qbancoffee/coco_motherboards/26-313xB/3d_models/channel_switch.stp

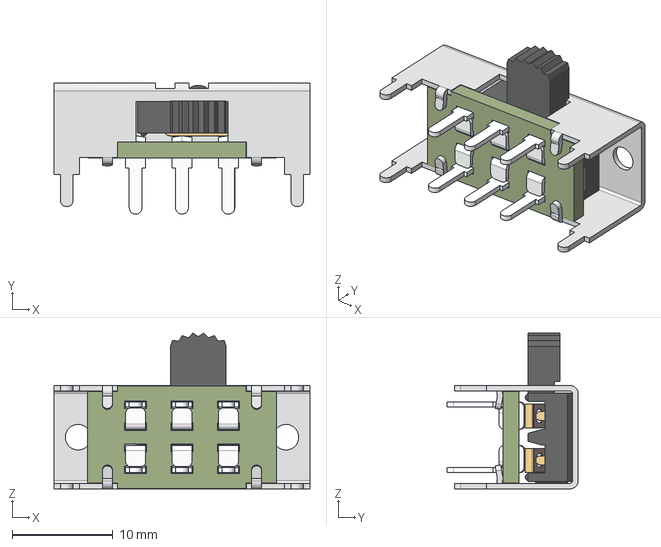
[picture p18: CAD file, 2022-07-08]
26-313xB/3d_models/channel_switch.stp
25.4 x 13.0 x 15.5 mm
