qbancoffee/coco_motherboards/26-313xB/3d_models/keyboard_connector.stp

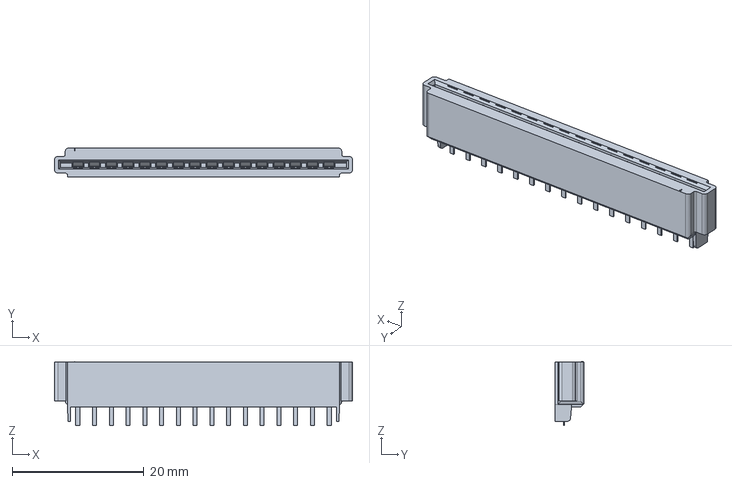
[picture p19: CAD file, 2022-07-08]
26-313xB/3d_models/keyboard_connector.stp
45.2 x 4.39 x 9.73 mm
