qbancoffee/coco_motherboards/26-313xB/3d_models/power_post.STEP

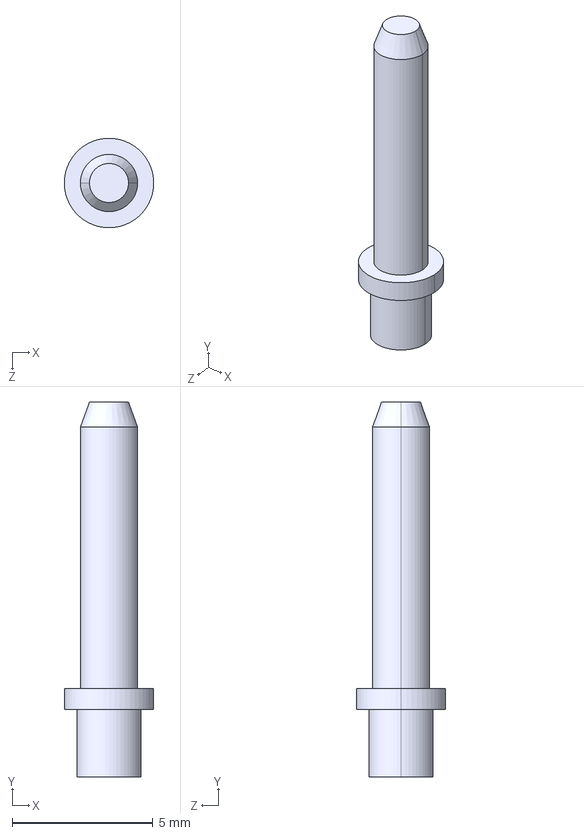
[picture p20: CAD file, 2022-07-08]
26-313xB/3d_models/power_post.STEP
3.18 x 13.3 x 3.18 mm
