qbancoffee/coco_motherboards/26-313xA/coco2/coco2.sch

## KiCad design 26-313xA/coco2/coco2.sch (2022-08-04)

Schematic: coco2.sch

Parts:
C1: .1uF; C_Disc_D4.7mm_W2.5mm_P5.00mm; Manufacturer part# RDER71H104K0K1H03B
CN1: Conn_02x20_Odd_Even; EBC20DRAS; Manufacturer part# EBC20DRAS
H999002, H999003: MountingHole; MountingHole_4mm
LOGO1: coco2_3134x_layout; coco2_3134A_layout
LOGO2: coco2_3134x_layout_top; coco2_3134A_layout_top
LOGO3: Logo_Open_Hardware_Large; OSHW-Logo2_7.3x6mm_SilkScreen
