qbancoffee/coco_motherboards/26-313xA/coco2/cpu.sch

## KiCad design 26-313xA/coco2/cpu.sch (2022-08-04)

Schematic: cpu.sch

Parts:
C8: 1uF 50V; CP_Radial_D5.0mm_P2.00mm; Manufacturer part# 515D105M050JA6AE3
C9: 100uF 16v; CP_Radial_D8.0mm_P5.00mm; Manufacturer part# ECA-1CM101B
C10, C55: .1uF; C_Disc_D4.7mm_W2.5mm_P5.00mm; Manufacturer part# RDER71H104K0K1H03B
C14: 33pF; C_Rect_L7.2mm_W3.0mm_P5.00mm_FKS2_FKP2_MKS2_MKP2; Manufacturer part# FA28NP01H330JNU06
C15: 56pF; C_Rect_L7.2mm_W2.5mm_P5.00mm_FKS2_FKP2_MKS2_MKP2; Manufacturer part# RDE5C1H560J0M1H03A
IC1: MC6809E; DIP-40_W15.24mm_Socket; Manufacturer part# ED40DT
IC14: 74LS623; DIP-20_W7.62mm_Socket; Manufacturer part# SN74LS623N
R14: 100K; R_Axial_DIN0207_L6.3mm_D2.5mm_P10.16mm_Horizontal; Manufacturer part# CF14JT100K
R15, R16, R17, R18: 4.7K; R_Axial_DIN0207_L6.3mm_D2.5mm_P10.16mm_Horizontal; Manufacturer part# Stackpole Electronics Inc
