qbancoffee/coco_motherboards/26-313xA/coco2/dram.sch

## KiCad design 26-313xA/coco2/dram.sch (2022-08-06)

Schematic: dram.sch

Parts:
C5, C6: .1uF; C_Disc_D4.7mm_W2.5mm_P5.00mm; Manufacturer part# RDER71H104K0K1H03B
CN3, CN4: Conn_01x12_Female; PinSocket_1x12_P2.54mm_for_memory_board_adapter; Manufacturer part# 0022182121
FB6: Ferrite_Bead_Small; ferrite_bead; Manufacturer part# 2743007111
IC10, IC11: TMS4416; DIP-18_W7.62mm_Socket; Manufacturer part# A 18-LC-TT
