qbancoffee/coco_motherboards/26-313xA/coco2/peripherals.sch

## KiCad design 26-313xA/coco2/peripherals.sch (2022-08-04)

Schematic: peripherals.sch

Parts:
C2, C18, C35, C44: .1uF; C_Disc_D4.7mm_W2.5mm_P5.00mm; Manufacturer part# RDER71H104K0K1H03B
C24, C25: 1800pF; C_Disc_D4.7mm_W2.5mm_P5.00mm; Manufacturer part# FA28C0G1H182JNU06
C26, C27, C28, C29, C30, C33: .022uF; C_Disc_D8.0mm_W2.5mm_P5.00mm; Manufacturer part# C317C223M5U5TA7301
C32: 10uF NP; C_Radial_D5.0mm_H11.0mm_P2.00mm; Manufacturer part# UES1E100MDM1TD
C34: 100uF 16v; CP_Radial_D8.0mm_P5.00mm; Manufacturer part# UST1C101MDD1TA
C36: 4700uF 16V; CP_Radial_D16.0mm_P7.50mm; Manufacturer part# 16YXJ4700M16X25
CN2: Conn_01x16_Female; PinHeader_1x16_P2.54mm_Vertical; Manufacturer part# 6-520415-6
D4, D12, D13: 1N4148; D_DO-35_SOD27_P7.62mm_Horizontal; Manufacturer part# 1N4148
D5, D6: 1KF20-04; D_A-405_P10.16mm_Horizontal; Manufacturer part# 1N4148
IC4: 6821; DIP-40_W15.24mm_Socket; Manufacturer part# ED40DT
IC5: SC67331P; DIP-40_W15.24mm_Socket; Manufacturer part# ED40DT
IC6: SC77526; DIP-20_W7.62mm_Socket; Manufacturer part# 243-20-1-03
IC7: SC77527P; DIP-16_W7.62mm_Socket; Manufacturer part# 1-2199298-4
J6: SolderJumper_2_Open; SolderJumper-2_P1.3mm_Open_RoundedPad1.0x1.5mm
J7: Conn_01x08; PinHeader_1x08_P2.54mm_Vertical
JK1: Right Joystick; CUI_SDS-60J; Manufacturer part# SDS-60J
JK2: Left Joystick; CUI_SDS-60J; Manufacturer part# SDS-60J
JK3: RS232; CUI_SDS-40J; Manufacturer part# SDS-40J
JK4: Cassette; CUI_SDS-50J; Manufacturer part# SDS-50J
Q1: KSD880O; TO-220-3_Horizontal_TabDown; Manufacturer part# KSD880O
R1, R2, R3, R4, R9: 10k; R_Axial_DIN0207_L6.3mm_D2.5mm_P10.16mm_Horizontal; Manufacturer part# CF14JT10K0
R5: 100 1/2W; R_Axial_DIN0411_L9.9mm_D3.6mm_P12.70mm_Horizontal; Manufacturer part# CF12JT100R
R10: 4.7K; R_Axial_DIN0207_L6.3mm_D2.5mm_P10.16mm_Horizontal; Manufacturer part# Stackpole Electronics Inc
R22: 510; R_Axial_DIN0207_L6.3mm_D2.5mm_P10.16mm_Horizontal; Manufacturer part# CF14JT510R
R23: 220 1/2W; R_Axial_DIN0411_L9.9mm_D3.6mm_P12.70mm_Horizontal; Manufacturer part# CF12JT220R
R24: 51; R_Axial_DIN0207_L6.3mm_D2.5mm_P10.16mm_Horizontal; Manufacturer part# CF1/4CT52R510J
R25: .1 ohms 1W; R_Axial_DIN0309_L9.0mm_D3.2mm_P12.70mm_Horizontal; Manufacturer part# RSMF1JTR100
R26, R27: 1K; R_Axial_DIN0207_L6.3mm_D2.5mm_P10.16mm_Horizontal; Manufacturer part# CF14JT1K00
R28: 270 1/2W; R_Axial_DIN0204_L3.6mm_D1.6mm_P7.62mm_Horizontal; Manufacturer part# SFR16S0002700JA500
RY1: J0971CS5VDC.45; RELAY_J0971CS5VDC.45; Manufacturer part# J0971CS5VDC.45

Notes on the sheet:
The SALT chip (Supply and Level Translator)
is responsible for supply regulation, RS-232
interface level translation, cassette read
operations, and driving the cassette relay.
http://roust-it.dk/coco/coco2_service_manual.pdf
D12 and D13 are in the schematic and the footprint is on the board but they are not installed.
