qbancoffee/coco_motherboards/26-313xA/coco2/power.sch

## KiCad design 26-313xA/coco2/power.sch (2022-08-06)

Schematic: power.sch

Parts:
A1: A1; power_connector_post; Manufacturer part# 6331-0-00-15-00-00-08-0
A2: A2; power_connector_post; Manufacturer part# 6331-0-00-15-00-00-08-0
A3: A3; power_connector_post; Manufacturer part# 6331-0-00-15-00-00-08-0
C7, C37, C39: .1uF; C_Disc_D4.7mm_W2.5mm_P5.00mm; Manufacturer part# RDER71H104K0K1H03B
C38: 220uF 16V; CP_Radial_D8.0mm_P5.00mm; Manufacturer part# URS1C221MPD1TA
C40, C41, C42, C43: .022uF; C_Disc_D8.0mm_W2.5mm_P5.00mm; Manufacturer part# C317C223M5U5TA7301
D1, D2, D3: 1N4148; D_DO-35_SOD27_P7.62mm_Horizontal; Manufacturer part# 1N4148
D8, D9: 1N4002; D_DO-41_SOD81_P10.16mm_Horizontal; Manufacturer part# 1N4002G-T
D10, D11: 1N5401; D_DO-201AD_P15.24mm_Horizontal; Manufacturer part# 1N5401G-T
FB1, FB2: Ferrite_Bead_Small; ferrite_bead; Manufacturer part# 2743007111
R13: 100K; R_Axial_DIN0207_L6.3mm_D2.5mm_P10.16mm_Horizontal; Manufacturer part# CF14JT100K
SW1: SW_DPDT_x2; F2UEE; Manufacturer part# F2UEE
SW3: Reset Switch; B3F3152; Manufacturer part# B3F-3152

Notes on the sheet:
Reset Circuit
