qbancoffee/coco_motherboards/26-313xA/coco2/roms.sch

## KiCad design 26-313xA/coco2/roms.sch (2022-08-06)

Schematic: roms.sch

Parts:
C4: .1uF; C_Disc_D4.7mm_W2.5mm_P5.00mm; Manufacturer part# RDER71H104K0K1H03B
IC8: 27C128; DIP-28_W15.24mm_Socket; Manufacturer part# A 28-LC-TT
J1, J3, J4, J5: 128K 64K; SolderJumper-3_P1.3mm_Open_RoundedPad1.0x1.5mm_NumberLabels
J2: 64K 128K; SolderJumper-3_P1.3mm_Open_RoundedPad1.0x1.5mm_NumberLabels
JP8: SolderJumper_2_Open; SolderJumper-2_P1.3mm_Open_RoundedPad1.0x1.5mm
R20: 4.7K; R_Axial_DIN0207_L6.3mm_D2.5mm_P10.16mm_Horizontal; Manufacturer part# Stackpole Electronics Inc

Notes on the sheet:
J8 was added to either leave this pin floating or to set it low in order to use a 256kb EEPROM as well.
