qbancoffee/coco_motherboards/26-313xA/coco2/sam.sch

## KiCad design 26-313xA/coco2/sam.sch (2022-08-04)

Schematic: sam.sch

Parts:
C11: 100uF 16v; CP_Radial_D8.0mm_P5.00mm; Manufacturer part# UST1C101MDD1TA
C12, C16, C54, C99915: .1uF; C_Disc_D4.7mm_W2.5mm_P5.00mm; Manufacturer part# RDER71H104K0K1H03B
C13: 39pF; C_Disc_D7.5mm_W5.0mm_P5.00mm; Manufacturer part# RDE5C1H390J0M1H03A
C17: 56pF; C_Rect_L7.2mm_W2.5mm_P5.00mm_FKS2_FKP2_MKS2_MKP2; Manufacturer part# RDE5C1H560J0M1H03A
FB3, FB4, FB5: Ferrite_Bead_Small; ferrite_bead; Manufacturer part# 2743007111
IC2: SN74LS785N; DIP-40_W15.24mm_Socket; Manufacturer part# ED40DT
IC12: 74LS138; DIP-16_W7.62mm_Socket; Manufacturer part# 1-2199298-4
IC13: 74LS02; DIP-14_W7.62mm_Socket; Manufacturer part# 1-2199298-4
IC99913: 74LS02; DIP-14_W7.62mm_Socket; Manufacturer part# A 14-LC-TT
R11, R12, R29: 100; R_Axial_DIN0207_L6.3mm_D2.5mm_P10.16mm_Horizontal; Manufacturer part# MFR-25FBF52-100R
R19: 4.7K; R_Axial_DIN0207_L6.3mm_D2.5mm_P10.16mm_Horizontal; Manufacturer part# Stackpole Electronics Inc
R21: 1.5k; R_Axial_DIN0207_L6.3mm_D2.5mm_P10.16mm_Horizontal; Manufacturer part# MFR-25FBF52-1K5
R30, R31: 33; R_Axial_DIN0207_L6.3mm_D2.5mm_P10.16mm_Horizontal; Manufacturer part# CF14JT33R0
TC1: C_Variable; C_Rect_L7.2mm_W7.2mm_P5.00mm_FKS2_FKP2_MKS2_MKP2; Manufacturer part# GKG50015
X1: 14.31818 Mhz; Crystal_HC49-U_Horizontal; Manufacturer part# MP143

Notes on the sheet:
The original board cam with a 74LS02 piggy backed on on IC13 from Tandy. I added IC13X as the second chip that would have been piggy backed.
