qbancoffee/coco_motherboards/26-313xA/coco2/video.sch

## KiCad design 26-313xA/coco2/video.sch (2022-08-04)

Schematic: video.sch

Parts:
C19: 47uF 16v; CP_Radial_D5.0mm_P2.00mm; Manufacturer part# ULD1C470MDD1TD
C20, C22, C31, C56: .1uF; C_Disc_D4.7mm_W2.5mm_P5.00mm; Manufacturer part# RDER71H104K0K1H03B
C21, C23: 150pF; C_Rect_L7.2mm_W2.5mm_P5.00mm_FKS2_FKP2_MKS2_MKP2; Manufacturer part# FA28C0G2E151JNU06
C57, C59: .022uF; C_Disc_D8.0mm_W2.5mm_P5.00mm; Manufacturer part# C317C223M5U5TA7301
C58: .001uF; C_Rect_L4.0mm_W2.5mm_P2.50mm; Manufacturer part# C315C102K1R5TA7301
D7: 1KF20-04; D_A-405_P10.16mm_Horizontal; Manufacturer part# 1N4148
IC3: MC6847; DIP-40_W15.24mm_Socket; Manufacturer part# ED40DT
IC15: 74LS273; DIP-20_W7.62mm_Socket; Manufacturer part# 243-20-1-03
IC16: NE555P; DIP-8_W7.62mm_Socket; Manufacturer part# A 08-LC-TT
MDV-6: RF_modulator; CoCo_2_3134A_RF_Modulator
Q2: 2N3904; TO-92_Inline; Manufacturer part# PN2222A PBFREE
R6: 4.7K; R_Axial_DIN0207_L6.3mm_D2.5mm_P10.16mm_Horizontal; Manufacturer part# Stackpole Electronics Inc
R7: 150; R_Axial_DIN0207_L6.3mm_D2.5mm_P10.16mm_Horizontal; Manufacturer part# CF14JT150R
R8: 10k; R_Axial_DIN0207_L6.3mm_D2.5mm_P10.16mm_Horizontal; Manufacturer part# CF14JT10K0
R32: 1K; R_Axial_DIN0207_L6.3mm_D2.5mm_P10.16mm_Horizontal; Manufacturer part# CF14JT1K00
R33: 9.1k; R_Axial_DIN0207_L6.3mm_D2.5mm_P10.16mm_Horizontal; Manufacturer part# CF14JT9K10
R34: 2.2K; R_Axial_DIN0207_L6.3mm_D2.5mm_P10.16mm_Horizontal; Manufacturer part# MFR-25FRF52-2K2
SW2: Channel Switch; MFS201N-16-Z; Manufacturer part# MFS201N-16-Z
