qbancoffee/coco_motherboards/26-313xB/coco2/coco2.kicad_sch

## KiCad design 26-313xB/coco2/coco2.kicad_sch (2023-12-13)

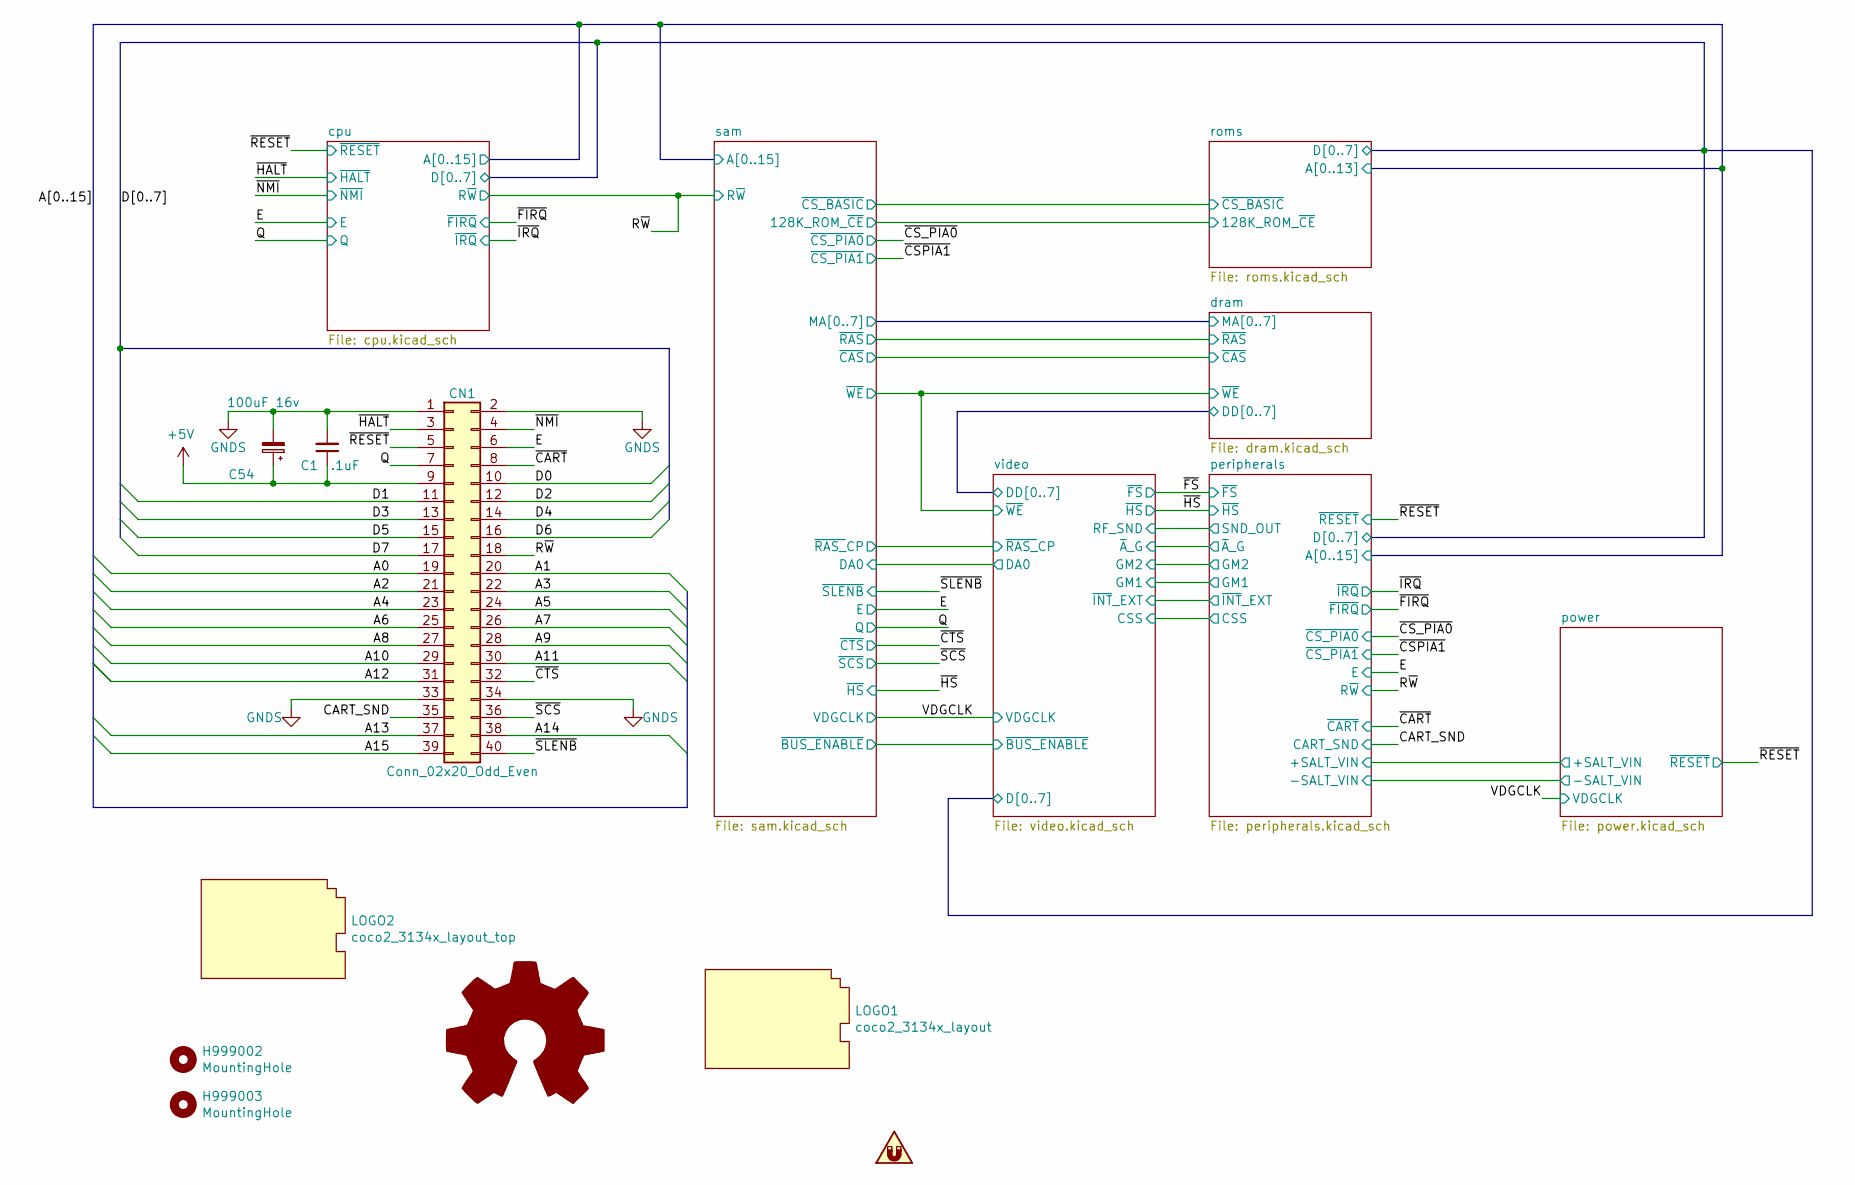
[picture p68: schematic coco2.kicad_sch]

Parts:
C1: .1uF; C_Disc_D4.7mm_W2.5mm_P5.00mm; Manufacturer part# RDER71H104K0K1H03B
C54: 100uF 16v; CP_Radial_D8.0mm_P5.00mm; Manufacturer part# UST1C101MDD1TA
CN1: Conn_02x20_Odd_Even; EBC20DRAS; Manufacturer part# EBC20DRAS
H999002, H999003: MountingHole; MountingHole_4mm
LOGO1: coco2_3134x_layout; coco2_3134B_layout_bottom_a
LOGO2: coco2_3134x_layout_top; coco2_3134B_layout_top_a
LOGO3: Logo_Open_Hardware_Large; OSHW-Logo2_7.3x6mm_SilkScreen
LOGO4: SYM_Magnet_Small; gah

Connections:
+5V: C1.1, C54.1, CN1.9
A0: CN1.19
A1: CN1.20
A2: CN1.21
A3: CN1.22
A4: CN1.23
A5: CN1.24
A6: CN1.25
A7: CN1.26
A8: CN1.27
A9: CN1.28
A10: CN1.29
A11: CN1.30
A12: CN1.31
A13: CN1.37
A14: CN1.38
A15: CN1.39
CART_SND: CN1.35
D0: CN1.10
D1: CN1.11
D2: CN1.12
D3: CN1.13
D4: CN1.14
D5: CN1.15
D6: CN1.16
D7: CN1.17
E: CN1.6
GNDS: C1.2, C54.2, CN1.1, CN1.2, CN1.33, CN1.34
Q: CN1.7
R~W: CN1.18
~CART: CN1.8
~CTS: CN1.32
~HALT: CN1.3
~NMI: CN1.4
~RESET: CN1.5
~SCS: CN1.36
~SLENB: CN1.40
