qbancoffee/coco_motherboards/26-313xB/coco2/cpu.kicad_sch

## KiCad design 26-313xB/coco2/cpu.kicad_sch (2023-12-13)

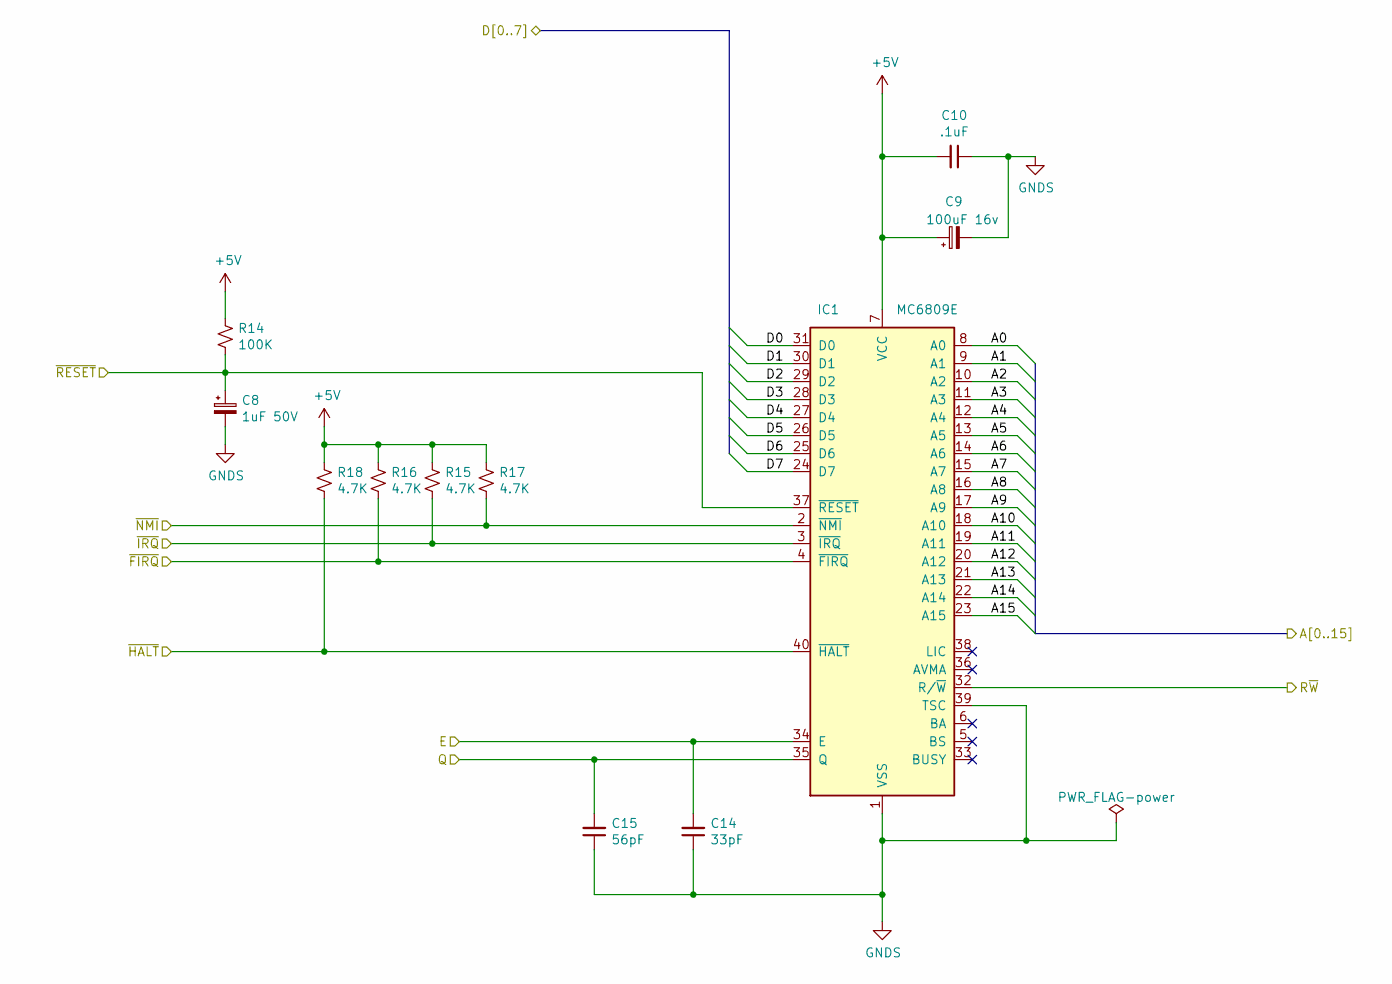
[picture p69: schematic cpu.kicad_sch]

Parts:
C8: 1uF 50V; CP_Radial_D5.0mm_P2.00mm; Manufacturer part# 515D105M050JA6AE3
C9: 100uF 16v; CP_Radial_D8.0mm_P5.00mm; Manufacturer part# ECA-1CM101B
C10: .1uF; C_Disc_D4.7mm_W2.5mm_P5.00mm; Manufacturer part# RDER71H104K0K1H03B
C14: 33pF; C_Rect_L7.2mm_W3.0mm_P5.00mm_FKS2_FKP2_MKS2_MKP2; Manufacturer part# FA28NP01H330JNU06
C15: 56pF; C_Rect_L7.2mm_W2.5mm_P5.00mm_FKS2_FKP2_MKS2_MKP2; Manufacturer part# RDE5C1H560J0M1H03A
IC1: MC6809E; DIP-40_W15.24mm_Socket; Manufacturer part# ED40DT
R14: 100K; R_Axial_DIN0207_L6.3mm_D2.5mm_P10.16mm_Horizontal; Manufacturer part# CF14JT100K
R15, R16, R17, R18: 4.7K; R_Axial_DIN0207_L6.3mm_D2.5mm_P10.16mm_Horizontal; Manufacturer part# Stackpole Electronics Inc

Connections:
+5V: C9.1, C10.2, IC1.7 (VCC), R14.1, R15.1, R16.1, R17.1, R18.1
A0: IC1.8 (A0)
A1: IC1.9 (A1)
A2: IC1.10 (A2)
A3: IC1.11 (A3)
A4: IC1.12 (A4)
A5: IC1.13 (A5)
A6: IC1.14 (A6)
A7: IC1.15 (A7)
A8: IC1.16 (A8)
A9: IC1.17 (A9)
A10: IC1.18 (A10)
A11: IC1.19 (A11)
A12: IC1.20 (A12)
A13: IC1.21 (A13)
A14: IC1.22 (A14)
A15: IC1.23 (A15)
D0: IC1.31 (D0)
D1: IC1.30 (D1)
D2: IC1.29 (D2)
D3: IC1.28 (D3)
D4: IC1.27 (D4)
D5: IC1.26 (D5)
D6: IC1.25 (D6)
D7: IC1.24 (D7)
E: C14.2, IC1.34 (E)
GNDS: C8.2, C9.2, C10.1, C14.1, C15.1, IC1.1 (VSS), IC1.39 (TSC)
Q: C15.2, IC1.35 (Q)
R~W: IC1.32 (R/~W)
~FIRQ: IC1.4 (~FIRQ), R16.2
~HALT: IC1.40 (~HALT), R18.2
~IRQ: IC1.3 (~IRQ), R15.2
~NMI: IC1.2 (~NMI), R17.2
~RESET: C8.1, IC1.37 (~RESET), R14.2
