qbancoffee/coco_motherboards/26-313xB/coco2/dram.kicad_sch

## KiCad design 26-313xB/coco2/dram.kicad_sch (2023-12-13)

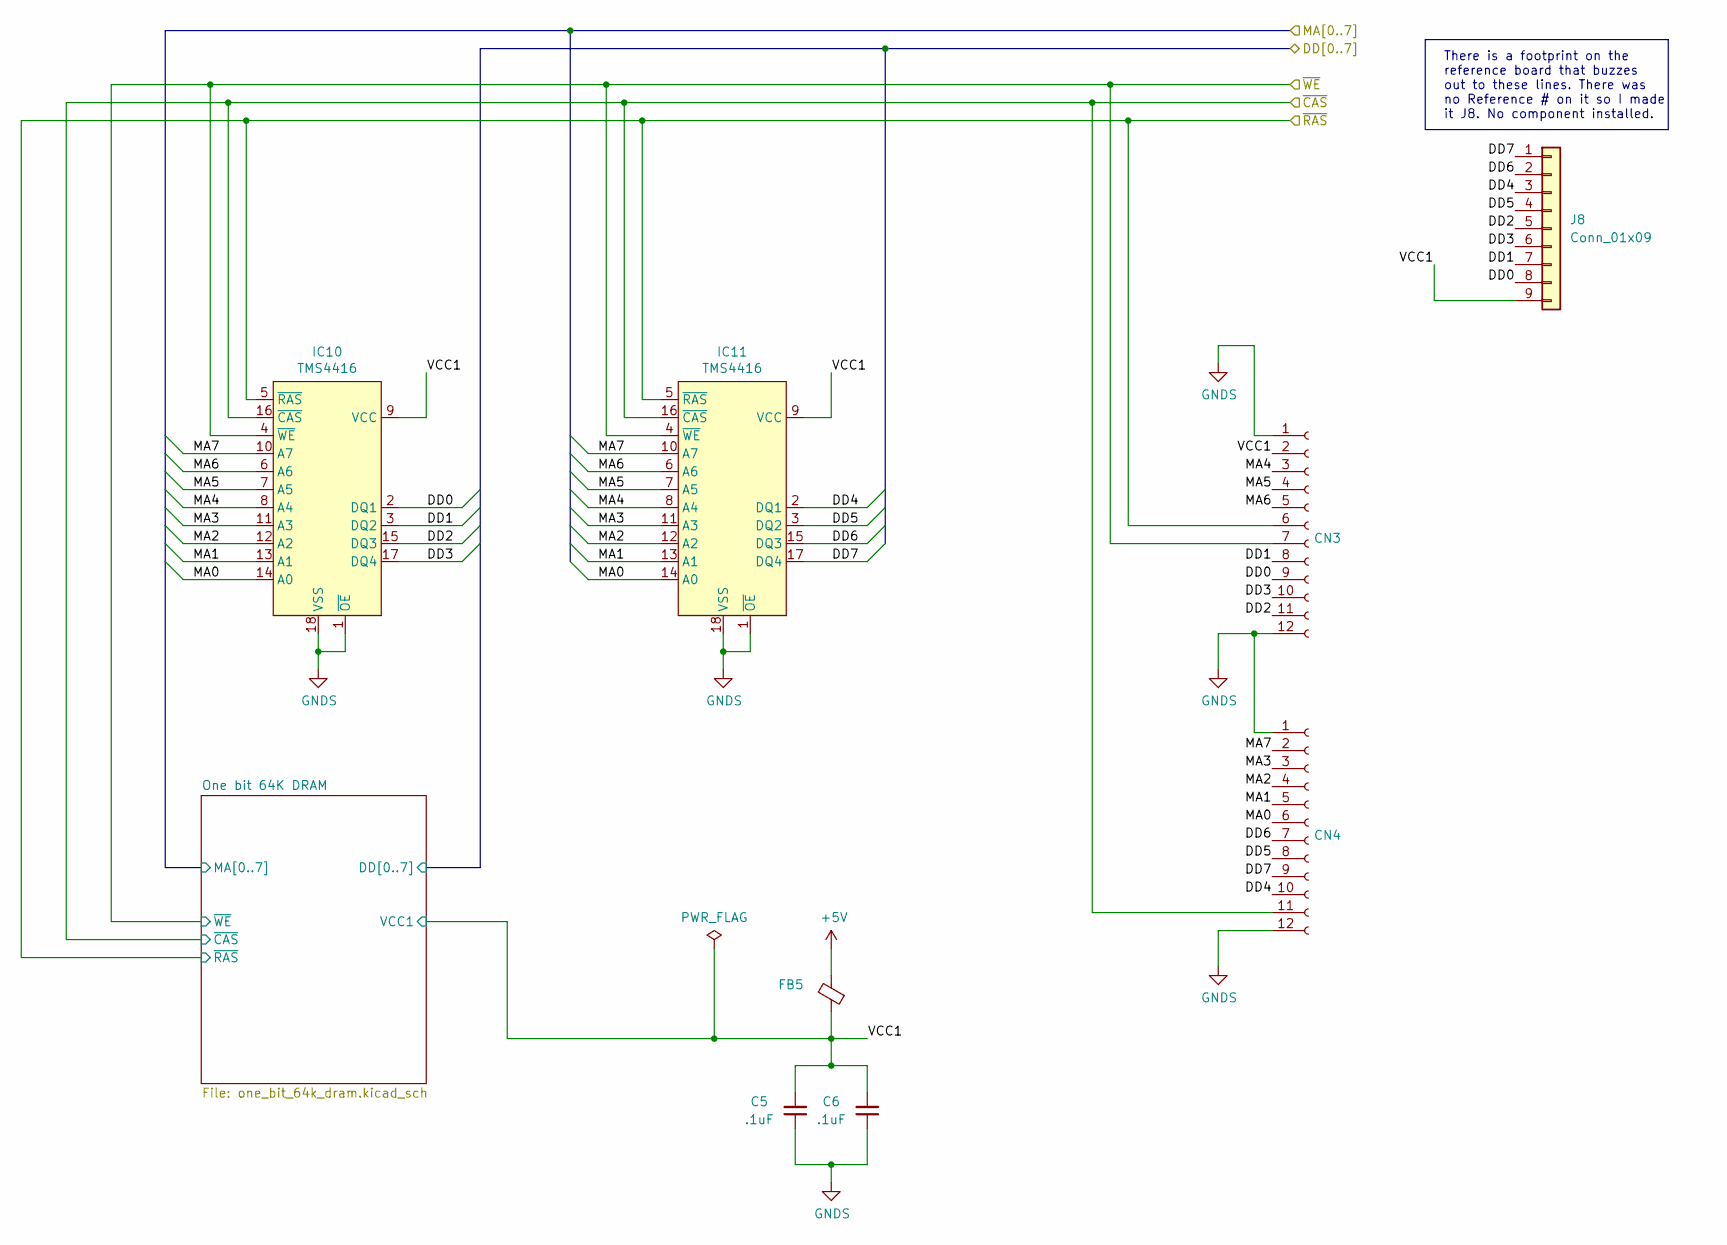
[picture p70: schematic dram.kicad_sch]

Parts:
C5, C6: .1uF; C_Disc_D4.7mm_W2.5mm_P5.00mm; Manufacturer part# RDER71H104K0K1H03B
CN3, CN4: Conn_01x12_Female; PinSocket_1x12_P2.54mm_for_memory_board_adapter; Manufacturer part# 0022182121
FB5: Ferrite_Bead_Small; ferrite_bead; Manufacturer part# 2743007111
IC10, IC11: TMS4416; DIP-18_W7.62mm_Socket; Manufacturer part# A 18-LC-TT
J8: Conn_01x09; PinHeader_1x09_P2.54mm_Vertical

Connections:
+5V: FB5.2
DD0: CN3.9, IC10.2 (DQ1), J8.8
DD1: CN3.8, IC10.3 (DQ2), J8.7
DD2: CN3.11, IC10.15 (DQ3), J8.5
DD3: CN3.10, IC10.17 (DQ4), J8.6
DD4: CN4.10, IC11.2 (DQ1), J8.3
DD5: CN4.8, IC11.3 (DQ2), J8.4
DD6: CN4.7, IC11.15 (DQ3), J8.2
DD7: CN4.9, IC11.17 (DQ4), J8.1
GNDS: C5.1, C6.1, CN3.1, CN3.12, CN4.1, CN4.12, IC10.1 (~OE), IC10.18 (VSS), IC11.1 (~OE), IC11.18 (VSS)
MA0: CN4.6, IC10.14 (A0), IC11.14 (A0)
MA1: CN4.5, IC10.13 (A1), IC11.13 (A1)
MA2: CN4.4, IC10.12 (A2), IC11.12 (A2)
MA3: CN4.3, IC10.11 (A3), IC11.11 (A3)
MA4: CN3.3, IC10.8 (A4), IC11.8 (A4)
MA5: CN3.4, IC10.7 (A5), IC11.7 (A5)
MA6: CN3.5, IC10.6 (A6), IC11.6 (A6)
MA7: CN4.2, IC10.10 (A7), IC11.10 (A7)
VCC1: C5.2, C6.2, CN3.2, FB5.1, IC10.9 (VCC), IC11.9 (VCC), J8.9
~CAS: CN4.11, IC10.16 (~CAS), IC11.16 (~CAS)
~RAS: CN3.6, IC10.5 (~RAS), IC11.5 (~RAS)
~WE: CN3.7, IC10.4 (~WE), IC11.4 (~WE)

Notes on the sheet:
There is a footprint on the reference board that buzzes out to these lines. There was no Reference # on it so I made it J8. No component installed.
