qbancoffee/coco_motherboards/26-313xB/coco2/one_bit_64k_dram.kicad_sch

## KiCad design 26-313xB/coco2/one_bit_64k_dram.kicad_sch (2023-12-13)

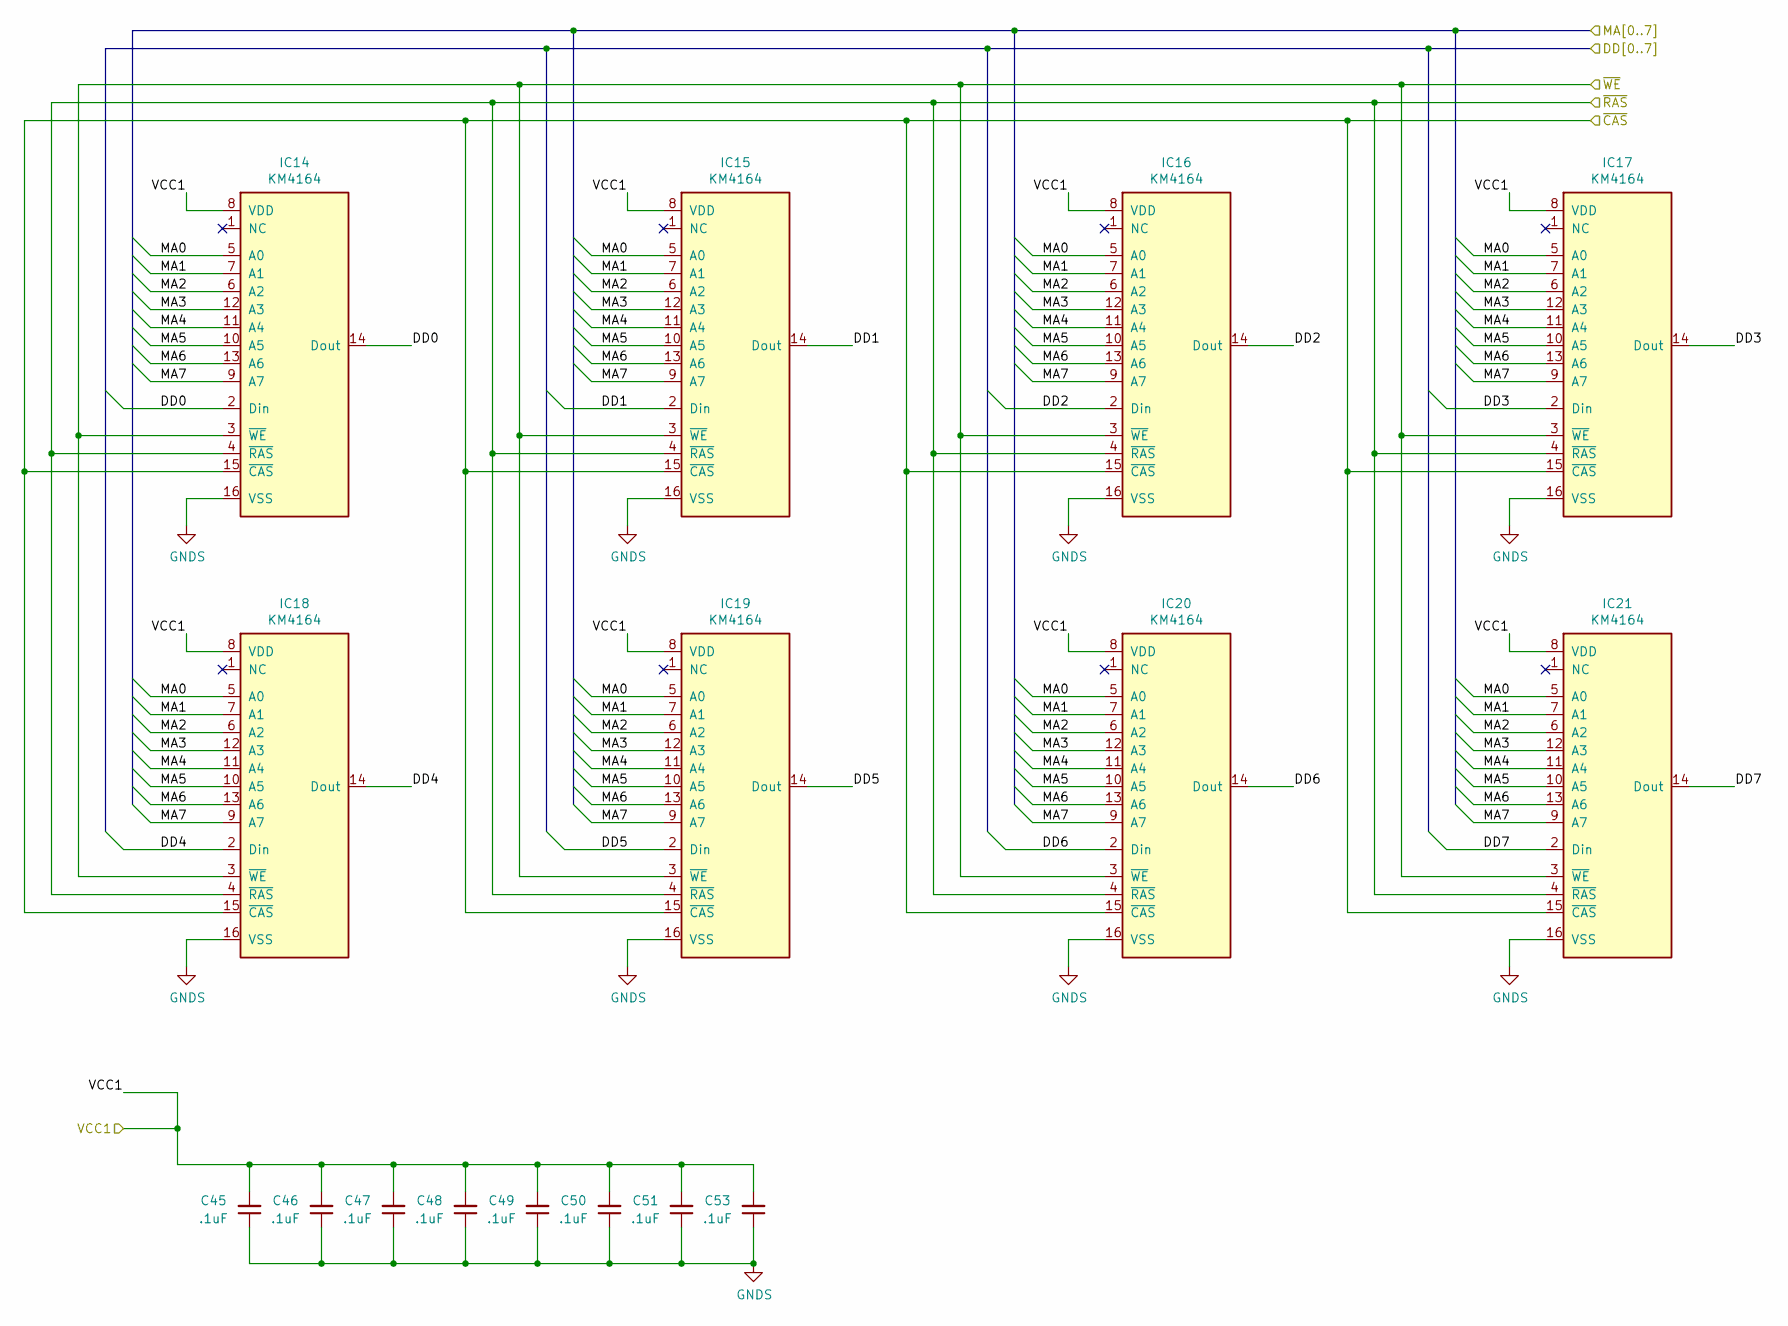
[picture p71: schematic one_bit_64k_dram.kicad_sch]

Parts:
C45, C46, C47, C48, C49, C50, C51, C53: .1uF; C_Disc_D4.7mm_W2.5mm_P5.00mm; Manufacturer part# RDER71H104K0K1H03B
IC14, IC15, IC16, IC17, IC18, IC19, IC20, IC21: KM4164; DIP-16_W7.62mm_Socket

Connections:
DD0: IC14.2 (Din), IC14.14 (Dout)
DD1: IC15.2 (Din), IC15.14 (Dout)
DD2: IC16.2 (Din), IC16.14 (Dout)
DD3: IC17.2 (Din), IC17.14 (Dout)
DD4: IC18.2 (Din), IC18.14 (Dout)
DD5: IC19.2 (Din), IC19.14 (Dout)
DD6: IC20.2 (Din), IC20.14 (Dout)
DD7: IC21.2 (Din), IC21.14 (Dout)
GNDS: C45.1, C46.1, C47.1, C48.1, C49.1, C50.1, C51.1, C53.1, IC14.16 (VSS), IC15.16 (VSS), IC16.16 (VSS), IC17.16 (VSS), IC18.16 (VSS), IC19.16 (VSS), IC20.16 (VSS), IC21.16 (VSS)
MA0: IC14.5 (A0), IC15.5 (A0), IC16.5 (A0), IC17.5 (A0), IC18.5 (A0), IC19.5 (A0), IC20.5 (A0), IC21.5 (A0)
MA1: IC14.7 (A1), IC15.7 (A1), IC16.7 (A1), IC17.7 (A1), IC18.7 (A1), IC19.7 (A1), IC20.7 (A1), IC21.7 (A1)
MA2: IC14.6 (A2), IC15.6 (A2), IC16.6 (A2), IC17.6 (A2), IC18.6 (A2), IC19.6 (A2), IC20.6 (A2), IC21.6 (A2)
MA3: IC14.12 (A3), IC15.12 (A3), IC16.12 (A3), IC17.12 (A3), IC18.12 (A3), IC19.12 (A3), IC20.12 (A3), IC21.12 (A3)
MA4: IC14.11 (A4), IC15.11 (A4), IC16.11 (A4), IC17.11 (A4), IC18.11 (A4), IC19.11 (A4), IC20.11 (A4), IC21.11 (A4)
MA5: IC14.10 (A5), IC15.10 (A5), IC16.10 (A5), IC17.10 (A5), IC18.10 (A5), IC19.10 (A5), IC20.10 (A5), IC21.10 (A5)
MA6: IC14.13 (A6), IC15.13 (A6), IC16.13 (A6), IC17.13 (A6), IC18.13 (A6), IC19.13 (A6), IC20.13 (A6), IC21.13 (A6)
MA7: IC14.9 (A7), IC15.9 (A7), IC16.9 (A7), IC17.9 (A7), IC18.9 (A7), IC19.9 (A7), IC20.9 (A7), IC21.9 (A7)
VCC1: C45.2, C46.2, C47.2, C48.2, C49.2, C50.2, C51.2, C53.2, IC14.8 (VDD), IC15.8 (VDD), IC16.8 (VDD), IC17.8 (VDD), IC18.8 (VDD), IC19.8 (VDD), IC20.8 (VDD), IC21.8 (VDD)
~CAS: IC14.15 (~CAS), IC15.15 (~CAS), IC16.15 (~CAS), IC17.15 (~CAS), IC18.15 (~CAS), IC19.15 (~CAS), IC20.15 (~CAS), IC21.15 (~CAS)
~RAS: IC14.4 (~RAS), IC15.4 (~RAS), IC16.4 (~RAS), IC17.4 (~RAS), IC18.4 (~RAS), IC19.4 (~RAS), IC20.4 (~RAS), IC21.4 (~RAS)
~WE: IC14.3 (~WE), IC15.3 (~WE), IC16.3 (~WE), IC17.3 (~WE), IC18.3 (~WE), IC19.3 (~WE), IC20.3 (~WE), IC21.3 (~WE)
