qbancoffee/coco_motherboards/26-313xB/coco2/sam.kicad_sch

## KiCad design 26-313xB/coco2/sam.kicad_sch (2023-12-13)

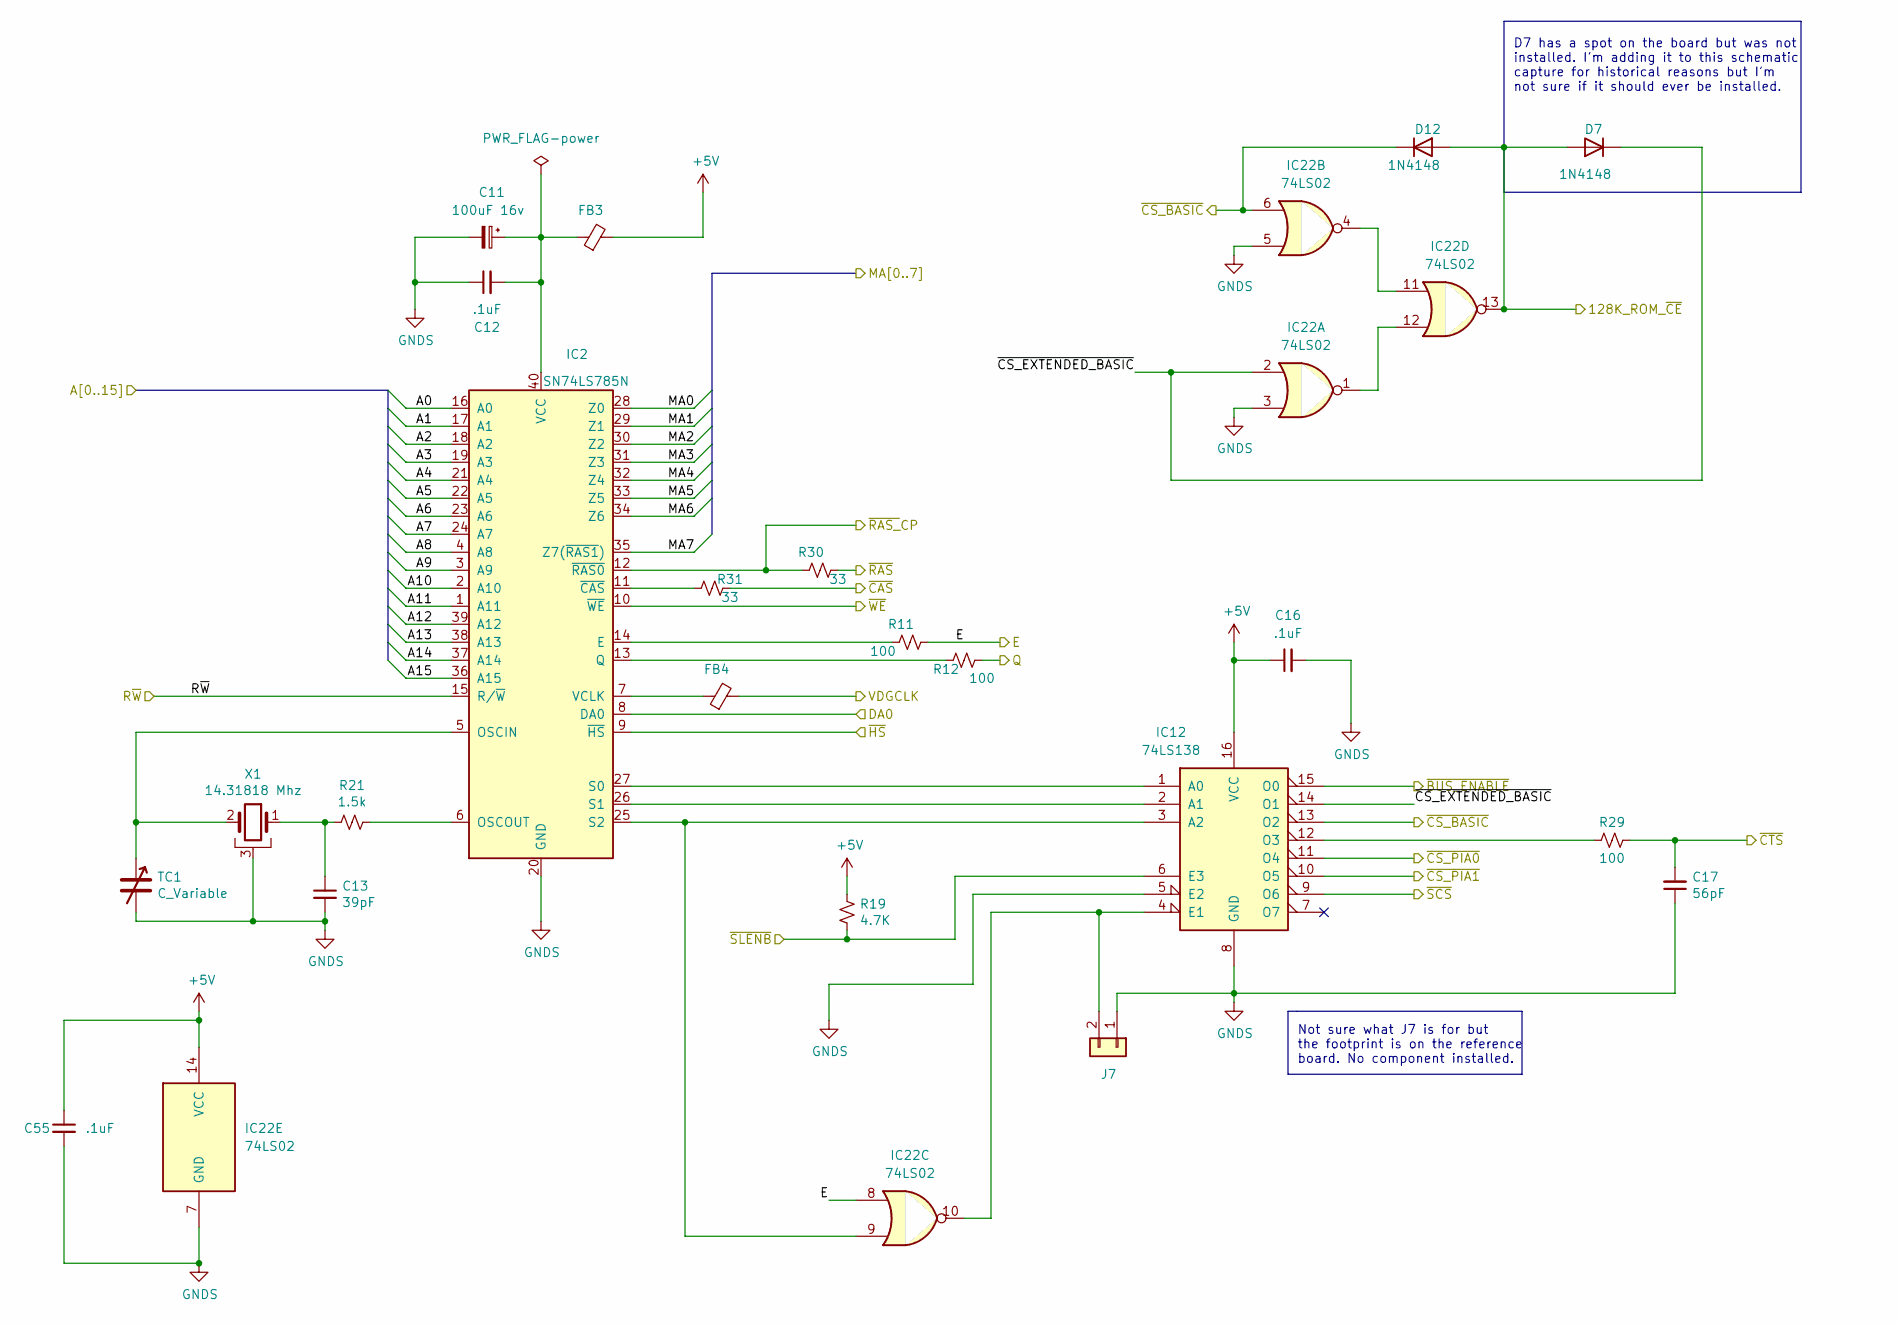
[picture p72: schematic sam.kicad_sch]

Parts:
C11: 100uF 16v; CP_Radial_D8.0mm_P5.00mm; Manufacturer part# UST1C101MDD1TA
C12, C16, C55: .1uF; C_Disc_D4.7mm_W2.5mm_P5.00mm; Manufacturer part# RDER71H104K0K1H03B
C13: 39pF; C_Disc_D7.5mm_W5.0mm_P5.00mm; Manufacturer part# RDE5C1H390J0M1H03A
C17: 56pF; C_Rect_L7.2mm_W2.5mm_P5.00mm_FKS2_FKP2_MKS2_MKP2; Manufacturer part# RDE5C1H560J0M1H03A
D7, D12: 1N4148; D_DO-35_SOD27_P7.62mm_Horizontal; Manufacturer part# 1N4148
FB3, FB4: Ferrite_Bead_Small; ferrite_bead; Manufacturer part# 2743007111
IC2: SN74LS785N; DIP-40_W15.24mm_Socket; Manufacturer part# ED40DT
IC12: 74LS138; DIP-16_W7.62mm_Socket; Manufacturer part# 1-2199298-4
IC22: 74LS02; DIP-14_W7.62mm_Socket
J7: Conn_01x02; PinHeader_1x02_P2.54mm_Vertical
R11, R12, R29: 100; R_Axial_DIN0207_L6.3mm_D2.5mm_P10.16mm_Horizontal; Manufacturer part# MFR-25FBF52-100R
R19: 4.7K; R_Axial_DIN0207_L6.3mm_D2.5mm_P10.16mm_Horizontal; Manufacturer part# Stackpole Electronics Inc
R21: 1.5k; R_Axial_DIN0207_L6.3mm_D2.5mm_P10.16mm_Horizontal; Manufacturer part# MFR-25FBF52-1K5
R30, R31: 33; R_Axial_DIN0207_L6.3mm_D2.5mm_P10.16mm_Horizontal; Manufacturer part# CF14JT33R0
TC1: C_Variable; C_Rect_L7.2mm_W7.2mm_P5.00mm_FKS2_FKP2_MKS2_MKP2; Manufacturer part# GKG50015
X1: 14.31818 Mhz; Crystal_HC49-U_Horizontal; Manufacturer part# MP143

Connections:
128K_ROM_~CE: D7.2 (A), D12.2 (A), IC22.13
+5V: C16.1, C55.1, FB3.2, IC12.16 (VCC), IC22.14 (VCC), R19.1
A0: IC2.16 (A0)
A1: IC2.17 (A1)
A2: IC2.18 (A2)
A3: IC2.19 (A3)
A4: IC2.21 (A4)
A5: IC2.22 (A5)
A6: IC2.23 (A6)
A7: IC2.24 (A7)
A8: IC2.4 (A8)
A9: IC2.3 (A9)
A10: IC2.2 (A10)
A11: IC2.1 (A11)
A12: IC2.39 (A12)
A13: IC2.38 (A13)
A14: IC2.37 (A14)
A15: IC2.36 (A15)
DA0: IC2.8 (DA0)
E: IC22.8, R11.1
GNDS: C11.2, C12.1, C13.2, C16.2, C17.1, C55.2, IC2.20 (GND), IC12.5 (E2), IC12.8 (GND), IC22.3, IC22.5, IC22.7 (GND), J7.1, TC1.2, X1.3
MA0: IC2.28 (Z0)
MA1: IC2.29 (Z1)
MA2: IC2.30 (Z2)
MA3: IC2.31 (Z3)
MA4: IC2.32 (Z4)
MA5: IC2.33 (Z5)
MA6: IC2.34 (Z6)
MA7: IC2.35 (Z7(~RAS1))
unnamed: C11.1, C12.2, FB3.1, IC2.40 (VCC)
unnamed: C13.1, R21.2, X1.1
unnamed: FB4.1, IC2.7 (VCLK)
unnamed: IC2.5 (OSCIN), TC1.1, X1.2
unnamed: IC2.6 (OSCOUT), R21.1
unnamed: IC2.11 (~CAS), R31.2
unnamed: IC2.13 (Q), R12.2
unnamed: IC2.14 (E), R11.2
unnamed: IC2.27 (S0), IC12.1 (A0)
unnamed: IC2.26 (S1), IC12.2 (A1)
unnamed: IC2.25 (S2), IC12.3 (A2), IC22.9
unnamed: IC12.4 (E1), IC22.10, J7.2
unnamed: IC12.12 (O3), R29.2
unnamed: IC22.1, IC22.12
unnamed: IC22.4, IC22.11
Q: R12.1
R~W: IC2.15 (R/~W)
VDGCLK: FB4.2
~BUS_ENABLE: IC12.15 (O0)
~CAS: R31.1
~CS_BASIC: D12.1 (K), IC12.13 (O2), IC22.6
~CS_EXTENDED_BASIC: D7.1 (K), IC12.14 (O1), IC22.2
~CS_PIA0: IC12.11 (O4)
~CS_PIA1: IC12.10 (O5)
~CTS: C17.2, R29.1
~HS: IC2.9 (~HS)
~RAS_CP: IC2.12 (~RAS0), R30.2
~RAS: R30.1
~SCS: IC12.9 (O6)
~SLENB: IC12.6 (E3), R19.2
~WE: IC2.10 (~WE)

Notes on the sheet:
Not sure what J7 is for but the footprint is on the reference board. No component installed.
D7 has a spot on the board but was not installed. I'm adding it to this schematic capture for historical reasons but I'm not sure if it should ever be installed.
