qbancoffee/coco_motherboards/26-313xB/coco2/video.kicad_sch

## KiCad design 26-313xB/coco2/video.kicad_sch (2023-12-13)

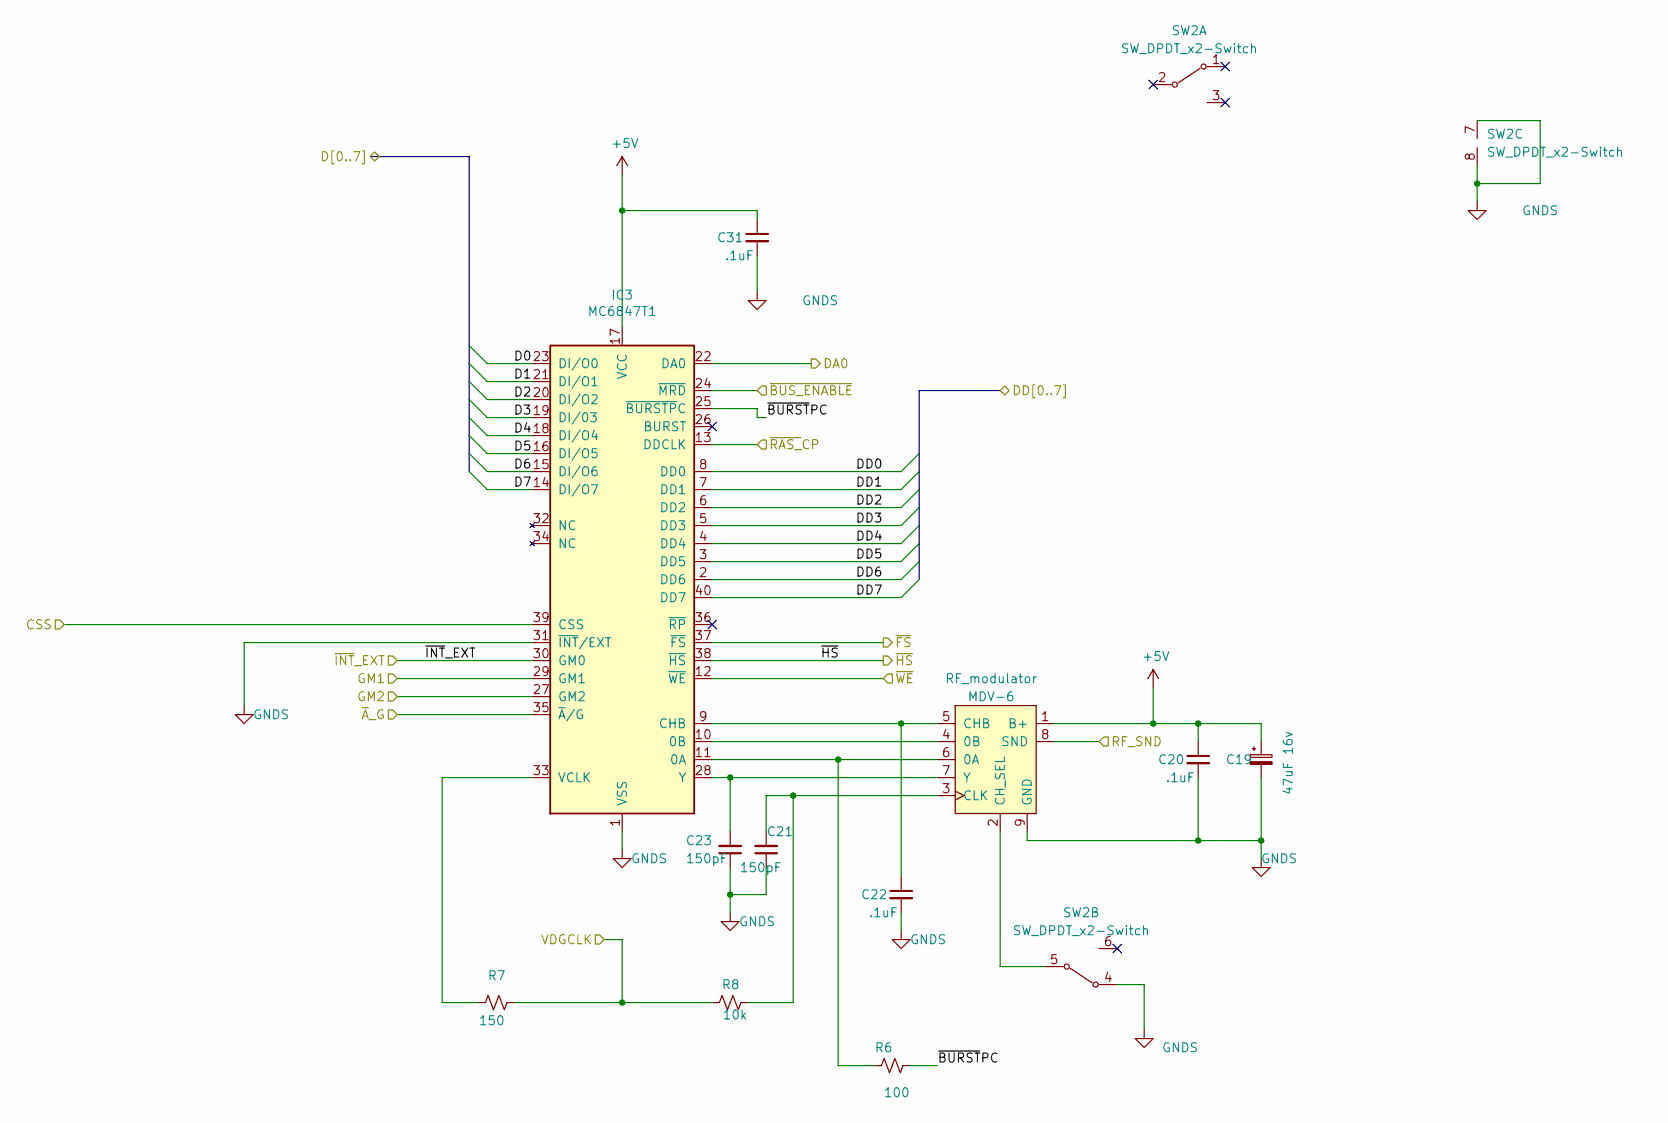
[picture p73: schematic video.kicad_sch]

Parts:
C19: 47uF 16v; CP_Radial_D5.0mm_P2.00mm; Manufacturer part# ULD1C470MDD1TD
C20, C22, C31: .1uF; C_Disc_D4.7mm_W2.5mm_P5.00mm; Manufacturer part# RDER71H104K0K1H03B
C21, C23: 150pF; C_Rect_L7.2mm_W2.5mm_P5.00mm_FKS2_FKP2_MKS2_MKP2; Manufacturer part# FA28C0G2E151JNU06
IC3: MC6847T1; DIP-40_W15.24mm_Socket
MDV-6: RF_modulator; CoCo_2_3134A_RF_Modulator
R6: 100; R_Axial_DIN0207_L6.3mm_D2.5mm_P10.16mm_Horizontal; Manufacturer part# MFR-25FBF52-100R
R7: 150; R_Axial_DIN0207_L6.3mm_D2.5mm_P10.16mm_Horizontal; Manufacturer part# CF14JT150R
R8: 10k; R_Axial_DIN0207_L6.3mm_D2.5mm_P10.16mm_Horizontal; Manufacturer part# CF14JT10K0
SW2: SW_DPDT_x2-Switch; MFS201N-16-Z; manufacturer part# MFS201N-16-Z

Connections:
+5V: C19.1, C20.1, C31.1, IC3.17 (VCC), MDV-6.1 (B+)
CSS: IC3.39 (CSS)
D0: IC3.23 (DI/O0)
D1: IC3.21 (DI/O1)
D2: IC3.20 (DI/O2)
D3: IC3.19 (DI/03)
D4: IC3.18 (DI/O4)
D5: IC3.16 (DI/O5)
D6: IC3.15 (DI/O6)
D7: IC3.14 (DI/O7)
DA0: IC3.22 (DA0)
DD0: IC3.8 (DD0)
DD1: IC3.7 (DD1)
DD2: IC3.6 (DD2)
DD3: IC3.5 (DD3)
DD4: IC3.4 (DD4)
DD5: IC3.3 (DD5)
DD6: IC3.2 (DD6)
DD7: IC3.40 (DD7)
GM1: IC3.29 (GM1)
GM2: IC3.27 (GM2)
GNDS: C19.2, C20.2, C21.1, C22.2, C23.1, C31.2, IC3.1 (VSS), IC3.31 (~INT/EXT), MDV-6.9 (GND), SW2.4 (A), SW2.7 (GNDS), SW2.8 (GNDS)
unnamed: C21.2, MDV-6.3 (CLK), R8.1
unnamed: C22.1, IC3.9 (CHB), MDV-6.5 (CHB)
unnamed: C23.2, IC3.28 (Y), MDV-6.7 (Y)
unnamed: IC3.10 (0B), MDV-6.4 (0B)
unnamed: IC3.11 (0A), MDV-6.6 (0A), R6.2
unnamed: IC3.33 (VCLK), R7.2
unnamed: MDV-6.2 (CH_SEL), SW2.5 (B)
RF_SND: MDV-6.8 (SND)
VDGCLK: R7.1, R8.2
~A_G: IC3.35 (~A/G)
~BURSTPC: IC3.25 (~BURSTPC), R6.1
~BUS_ENABLE: IC3.24 (~MRD)
~FS: IC3.37 (~FS)
~HS: IC3.38 (~HS)
~INT_EXT: IC3.30 (GM0)
~RAS_CP: IC3.13 (DDCLK)
~WE: IC3.12 (~WE)
